Badbird5907/flipper-thermal-camera/flipper-app/mlx90640/mlx90640_i2c.c

#include "mlx90640_i2c.h"

#include <furi.h>
#include <furi_hal.h>
#include <string.h>

#define TAG "MLX90640"

#define MLX90640_I2C_TIMEOUT_MS 100U
#define MLX90640_I2C_MAX_READ_WORDS 32U
#define MLX90640_READ_RETRIES   3U

static paramsMLX90640 mlx90640_params;
static bool mlx90640_params_ready = false;
static float mlx90640_emissivity = 0.95f;
static uint16_t mlx90640_frame_data[834];
static uint8_t mlx90640_subpages_ready = 0U;

static uint16_t mlx90640_bswap16(uint16_t value) {
    return (uint16_t)((value << 8) | (value >> 8));
}

void MLX90640_I2CInit(void) {
}

int MLX90640_I2CGeneralReset(void) {
    const uint8_t reset_cmd = 0x06;

    furi_hal_i2c_acquire(&furi_hal_i2c_handle_external);
    const bool ok =
        furi_hal_i2c_tx(&furi_hal_i2c_handle_external, 0x00, &reset_cmd, 1, MLX90640_I2C_TIMEOUT_MS);
    furi_hal_i2c_release(&furi_hal_i2c_handle_external);

    return ok ? 0 : -1;
}

int MLX90640_I2CRead(
    uint8_t slaveAddr,
    uint16_t startAddress,
    uint16_t nMemAddressRead,
    uint16_t* data) {
    furi_hal_i2c_acquire(&furi_hal_i2c_handle_external);

    for(uint16_t offset = 0; offset < nMemAddressRead; offset += MLX90640_I2C_MAX_READ_WORDS) {
        const uint16_t words_left = nMemAddressRead - offset;
        const uint16_t words_to_read = (words_left > MLX90640_I2C_MAX_READ_WORDS) ?
                                           MLX90640_I2C_MAX_READ_WORDS :
                                           words_left;
        const uint16_t read_address = startAddress + offset;
        uint8_t cmd[2] = {
            (uint8_t)(read_address >> 8),
            (uint8_t)(read_address & 0xFFU),
        };

        const uint8_t address = (uint8_t)(slaveAddr << 1);
        const bool tx_ok = furi_hal_i2c_tx_ext(
            &furi_hal_i2c_handle_external,
            address,
            false,
            cmd,
            sizeof(cmd),
            FuriHalI2cBeginStart,
            FuriHalI2cEndAwaitRestart,
            MLX90640_I2C_TIMEOUT_MS);
        const bool rx_ok = tx_ok && furi_hal_i2c_rx_ext(
            &furi_hal_i2c_handle_external,
            address,
            false,
            (uint8_t*)&data[offset],
            words_to_read * sizeof(uint16_t),
            FuriHalI2cBeginRestart,
            FuriHalI2cEndStop,
            MLX90640_I2C_TIMEOUT_MS);

        if(!rx_ok) {
            furi_hal_i2c_release(&furi_hal_i2c_handle_external);
            FURI_LOG_E(
                TAG,
                "I2C read failed: addr=0x%02X reg=0x%04X words=%u tx=%u",
                slaveAddr,
                read_address,
                words_to_read,
                tx_ok);
            return -1;
        }

        for(uint16_t i = offset; i < offset + words_to_read; i++) {
            data[i] = mlx90640_bswap16(data[i]);
        }
    }

    furi_hal_i2c_release(&furi_hal_i2c_handle_external);

    return 0;
}

int MLX90640_I2CWrite(uint8_t slaveAddr, uint16_t writeAddress, uint16_t data) {
    const uint8_t cmd[4] = {
        (uint8_t)(writeAddress >> 8),
        (uint8_t)(writeAddress & 0xFFU),
        (uint8_t)(data >> 8),
        (uint8_t)(data & 0xFFU),
    };

    furi_hal_i2c_acquire(&furi_hal_i2c_handle_external);
    const bool ok = furi_hal_i2c_tx(
        &furi_hal_i2c_handle_external,
        (uint8_t)(slaveAddr << 1),
        cmd,
        sizeof(cmd),
        MLX90640_I2C_TIMEOUT_MS);
    furi_hal_i2c_release(&furi_hal_i2c_handle_external);

    return ok ? 0 : -1;
}

void MLX90640_I2CFreqSet(int freq) {
    UNUSED(freq);
}

bool mlx90640_read_eeprom(uint16_t eeprom[MLX90640_EEPROM_DUMP_NUM]) {
    return MLX90640_DumpEE(MLX90640_I2C_ADDRESS, eeprom) == MLX90640_NO_ERROR;
}

bool mlx90640_extract_params(uint16_t* eeprom, paramsMLX90640* params) {
    const int status = MLX90640_ExtractParameters(eeprom, params);
    if(status != MLX90640_NO_ERROR) {
        FURI_LOG_E(
            TAG,
            "Parameter extraction failed: status=%d ee[0]=0x%04X ee[16]=0x%04X ee[32]=0x%04X ee[64]=0x%04X",
            status,
            eeprom[0],
            eeprom[16],
            eeprom[32],
            eeprom[64]);
        return false;
    }

    memcpy(&mlx90640_params, params, sizeof(mlx90640_params));
    mlx90640_params_ready = true;
    mlx90640_subpages_ready = 0U;
    return true;
}

bool mlx90640_configure(uint8_t refresh_rate) {
    if(MLX90640_SetRefreshRate(MLX90640_I2C_ADDRESS, refresh_rate) != MLX90640_NO_ERROR) {
        return false;
    }

    return MLX90640_SetChessMode(MLX90640_I2C_ADDRESS) == MLX90640_NO_ERROR;
}

void mlx90640_set_emissivity(float emissivity) {
    mlx90640_emissivity = emissivity;
}

bool mlx90640_read_frame(float frame[MLX90640_PIXEL_COUNT]) {
    if(!mlx90640_params_ready) {
        return false;
    }

    const bool needs_full_frame = mlx90640_subpages_ready != 0x03U;

    do {
        int status = MLX90640_FRAME_DATA_ERROR;
        for(uint8_t attempt = 0; attempt < MLX90640_READ_RETRIES; attempt++) {
            status = MLX90640_GetFrameData(MLX90640_I2C_ADDRESS, mlx90640_frame_data);
            if(status >= 0) {
                break;
            }
        }

        if(status < 0) {
            return false;
        }

        const float ta = MLX90640_GetTa(mlx90640_frame_data, &mlx90640_params);
        MLX90640_CalculateTo(
            mlx90640_frame_data, &mlx90640_params, mlx90640_emissivity, ta - 8.0f, frame);
        mlx90640_subpages_ready |= (uint8_t)(1U << (mlx90640_frame_data[833] & 1U));
    } while(needs_full_frame && mlx90640_subpages_ready != 0x03U);

    MLX90640_BadPixelsCorrection(
        mlx90640_params.brokenPixels, frame, 1, &mlx90640_params);
    MLX90640_BadPixelsCorrection(
        mlx90640_params.outlierPixels, frame, 1, &mlx90640_params);

    return mlx90640_subpages_ready == 0x03U;
}
